KKSSJJ1112/ZUTOMAYO_mirror_shooter/사진/4.jpg

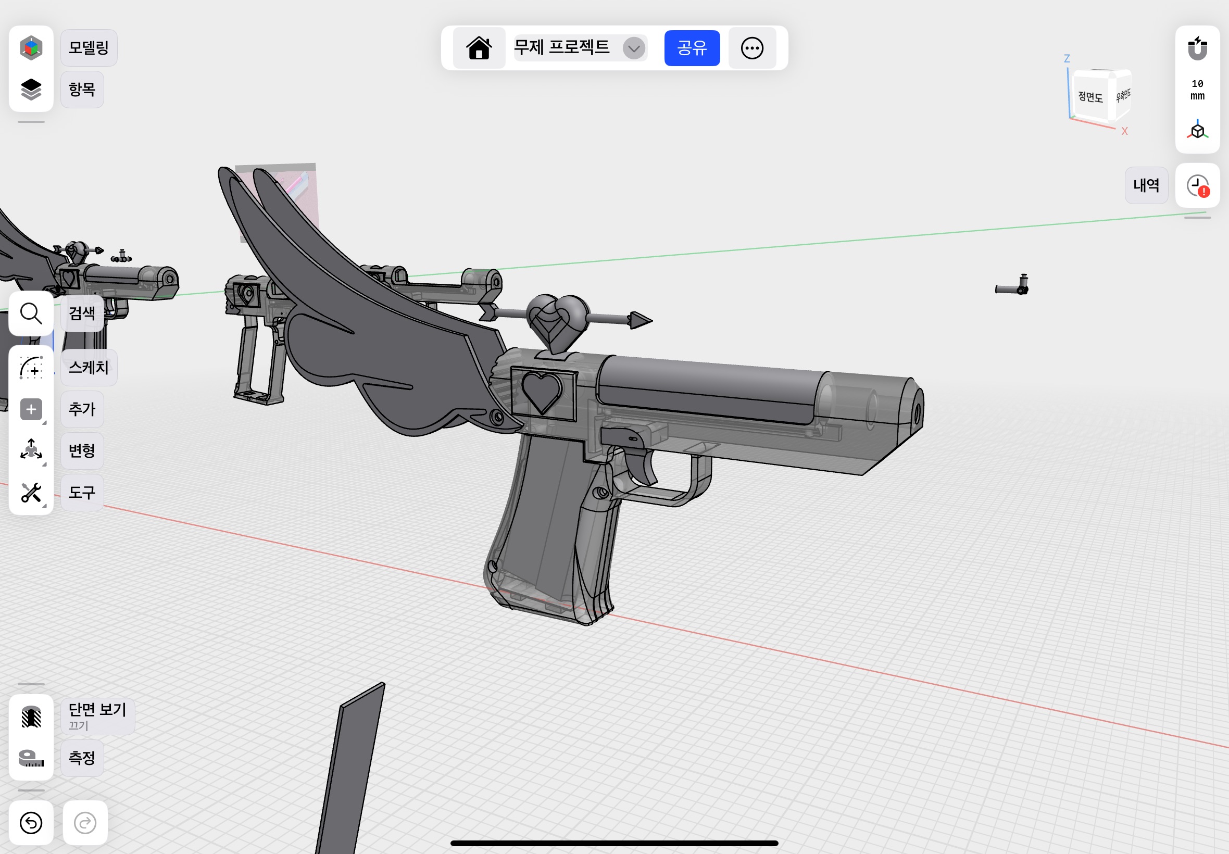
사진/4.jpg
