KKSSJJ1112/ZUTOMAYO_mirror_shooter/사진/6.jpg

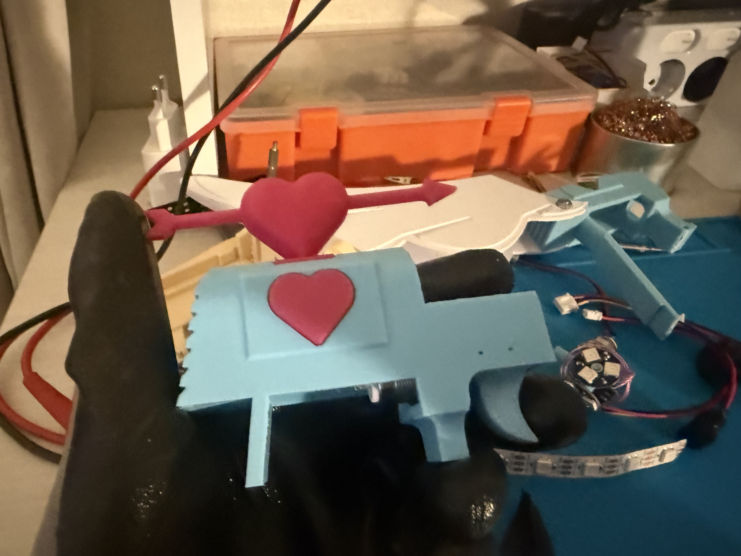
사진/6.jpg
