KKSSJJ1112/ZUTOMAYO_mirror_shooter/사진/8.jpg

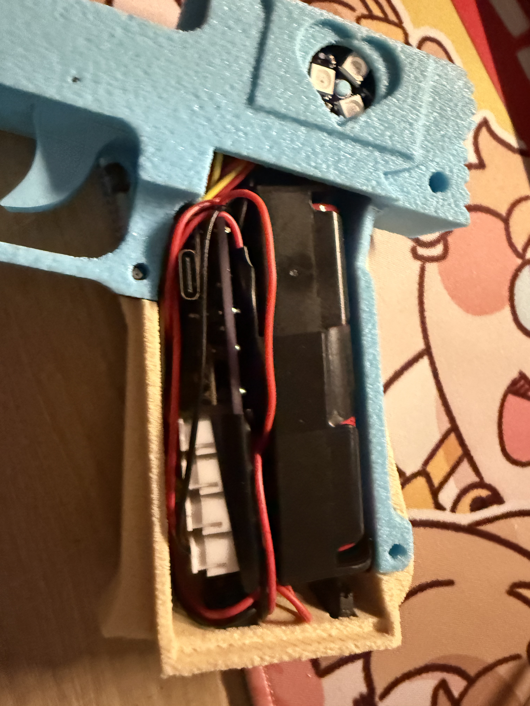
사진/8.jpg
