KKSSJJ1112/ZUTOMAYO_mirror_shooter/사진/ffa.png

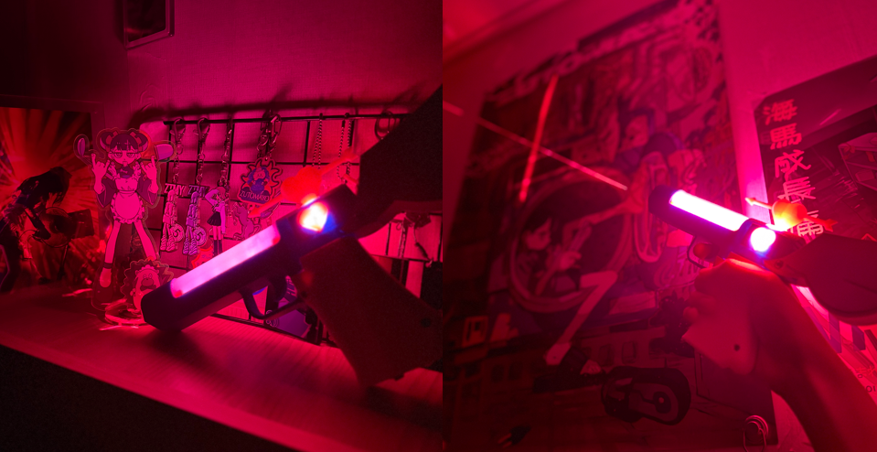
사진/ffa.png
