KKSSJJ1112/ZUTOMAYO_mirror_shooter/사진/KakaoTalk_20250901_193324154_01.jpg

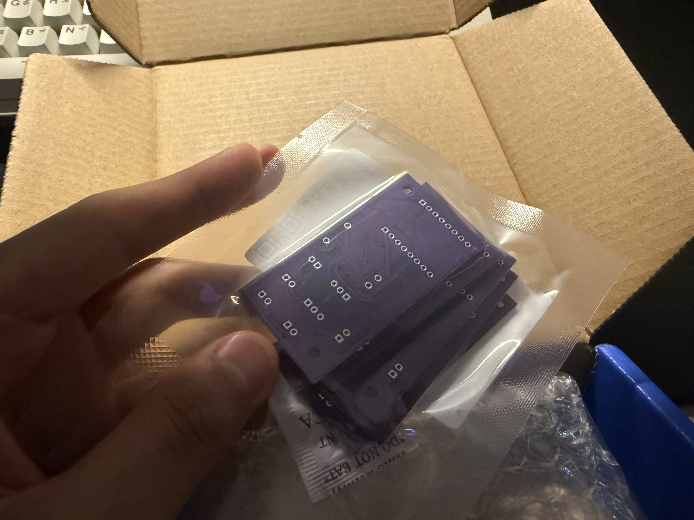
사진/KakaoTalk_20250901_193324154_01.jpg
