KKSSJJ1112/ZUTOMAYO_mirror_shooter/사진/KakaoTalk_20251231_225942691_02.jpg

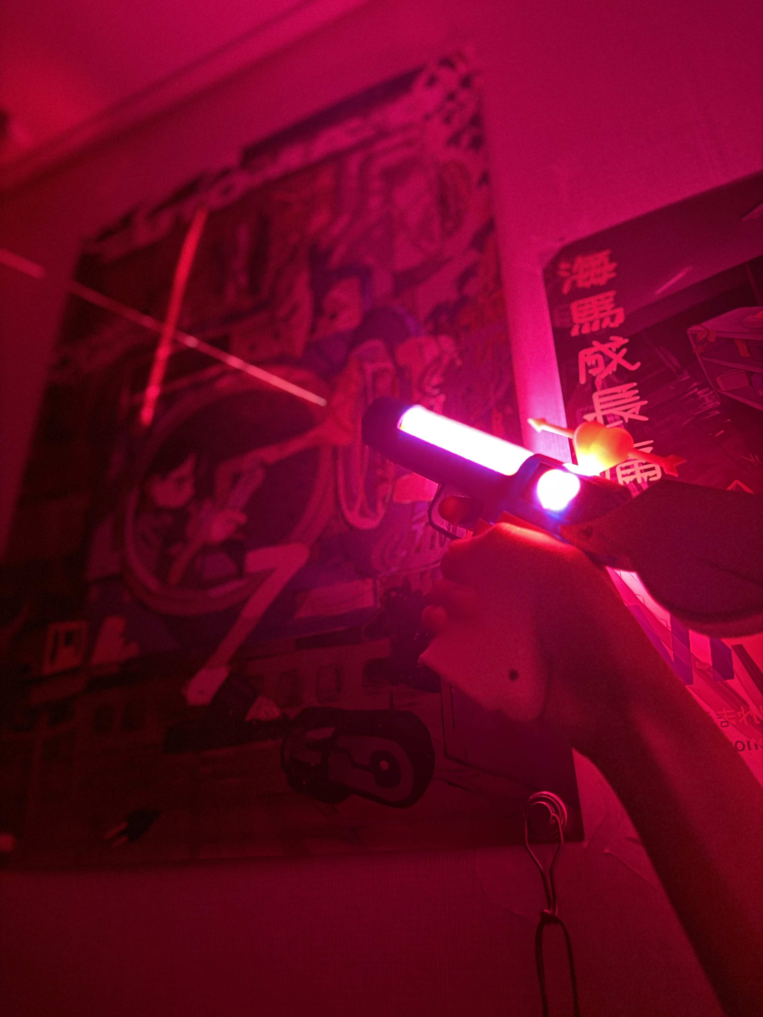
사진/KakaoTalk_20251231_225942691_02.jpg
