KKSSJJ1112/ZUTOMAYO_mirror_shooter/mirrorshooter_stl/____final/blue/ring holder.stl

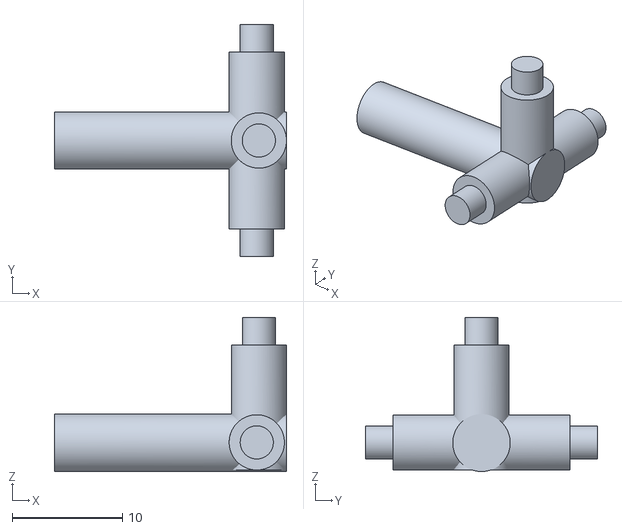
[picture p34: CAD file, 2025-11-05]
mirrorshooter_stl/____final/blue/ring holder.stl
21.0 x 21.0 x 13.9
