KKSSJJ1112/ZUTOMAYO_mirror_shooter/mirrorshooter_stl/____final/trans pink/small heart.stl

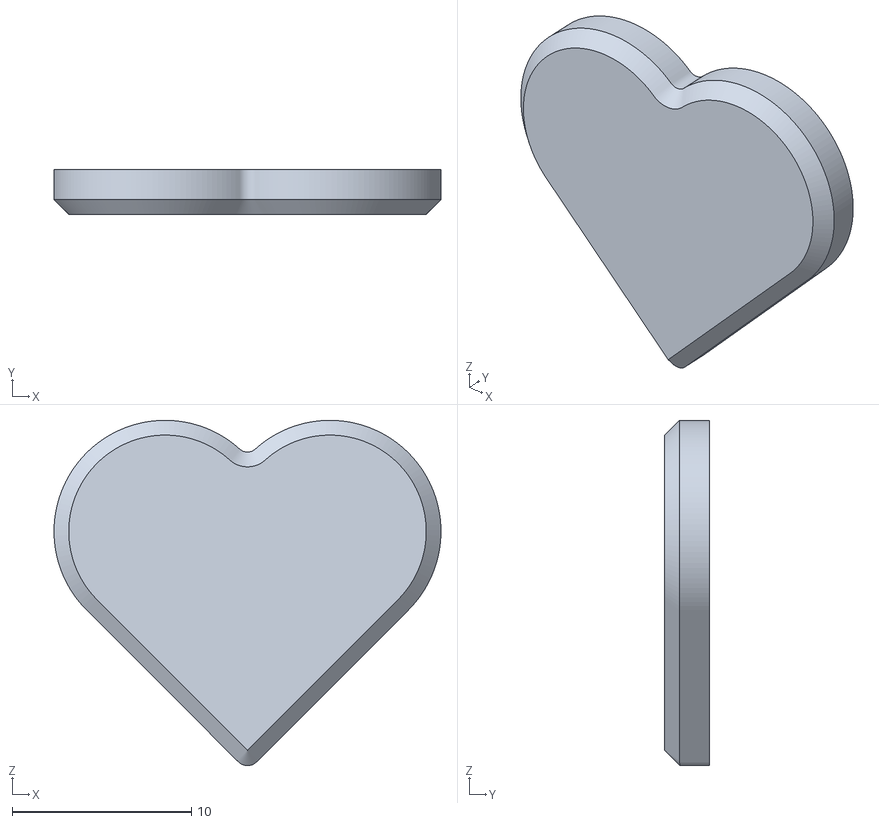
[picture p35: CAD file, 2025-11-05]
mirrorshooter_stl/____final/trans pink/small heart.stl
21.6 x 2.50 x 19.3
