KKSSJJ1112/ZUTOMAYO_mirror_shooter/mirrorshooter_stl/test/second_test/blue/ring holder ttesst.stl

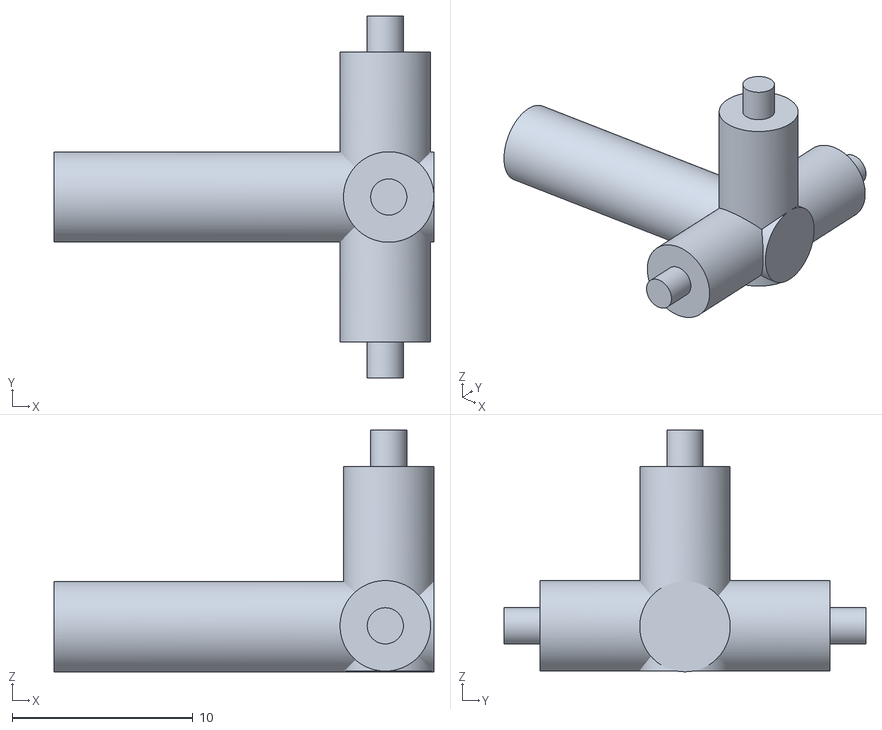
[picture p36: CAD file, 2025-11-05]
mirrorshooter_stl/test/second_test/blue/ring holder ttesst.stl
21.0 x 20.0 x 13.4
