KKSSJJ1112/ZUTOMAYO_mirror_shooter/mirrorshooter_stl/test/second_test/trans_pink/cover test.stl

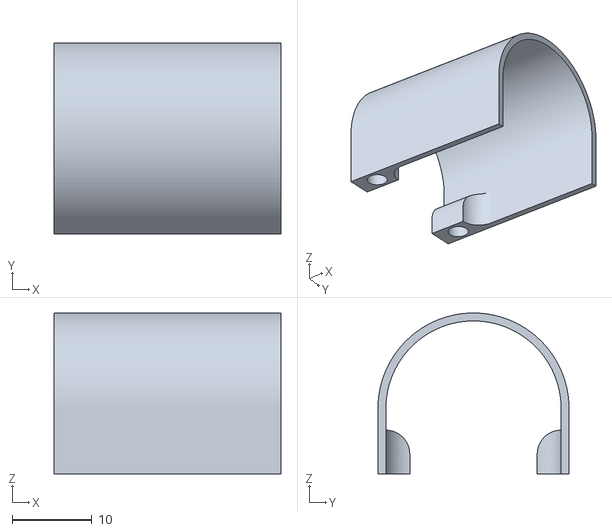
[picture p37: CAD file, 2025-11-05]
mirrorshooter_stl/test/second_test/trans_pink/cover test.stl
28.5 x 24.0 x 20.2
