KKSSJJ1112/ZUTOMAYO_mirror_shooter/mirrorshooter_stl/____final/trans pink/cover.stl

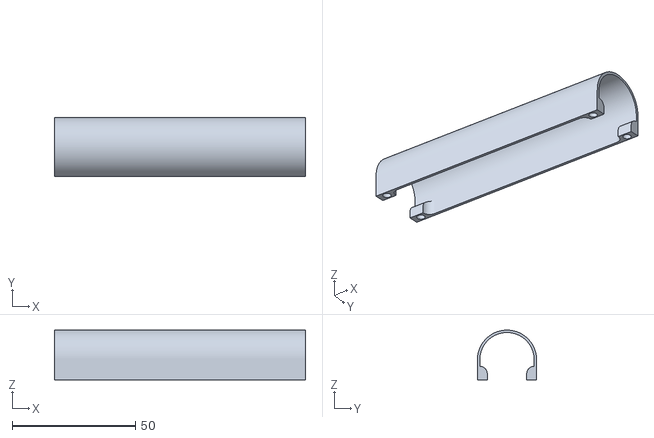
[picture p38: CAD file, 2025-11-05]
mirrorshooter_stl/____final/trans pink/cover.stl
101.8 x 24.0 x 20.2
