KKSSJJ1112/ZUTOMAYO_mirror_shooter/mirrorshooter_stl/test/first_test/trigger_test/triger-sub-invisible.stl

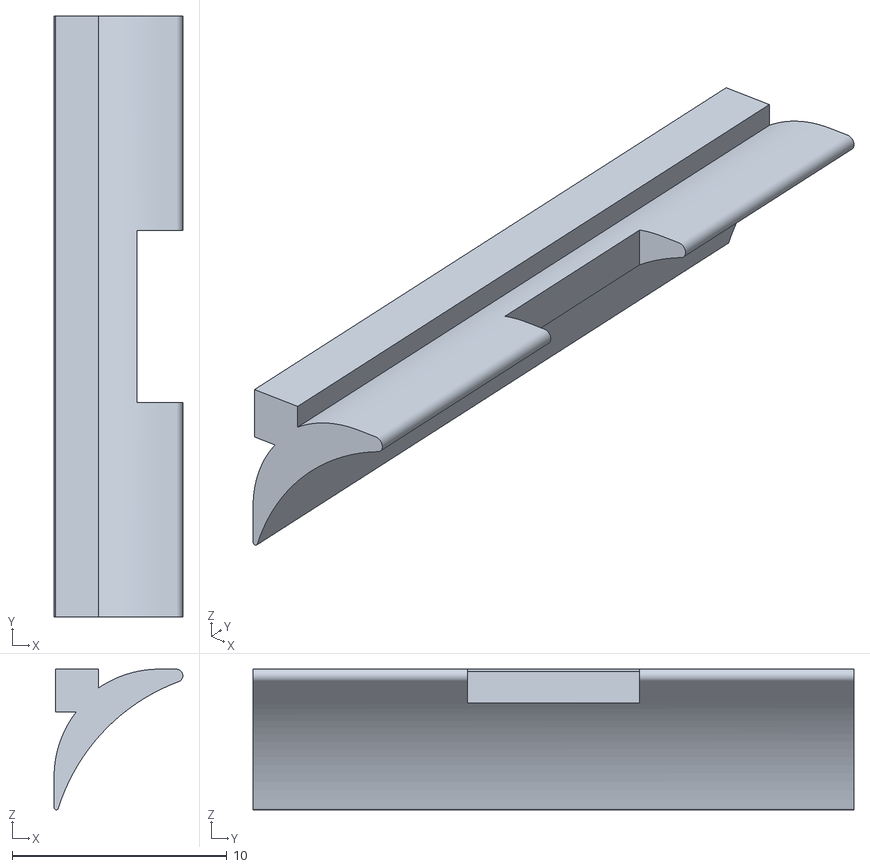
[picture p39: CAD file, 2025-11-05]
mirrorshooter_stl/test/first_test/trigger_test/triger-sub-invisible.stl
6.00 x 28.0 x 6.56
