KKSSJJ1112/ZUTOMAYO_mirror_shooter/mirrorshooter_stl/test/second_test/blue/trigger test.stl

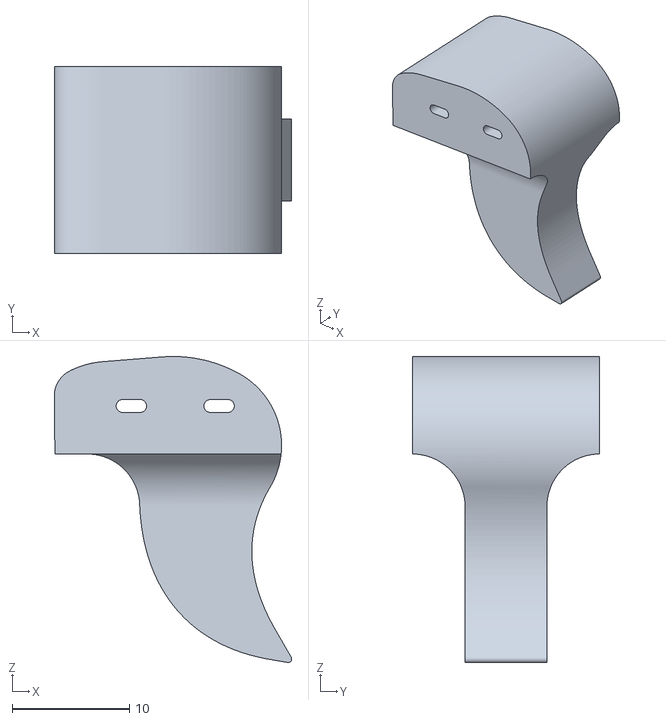
[picture p40: CAD file, 2025-11-05]
mirrorshooter_stl/test/second_test/blue/trigger test.stl
20.3 x 16.0 x 26.2
