KKSSJJ1112/ZUTOMAYO_mirror_shooter/mirrorshooter_stl/test/second_test/trans_pink/small heart test.stl

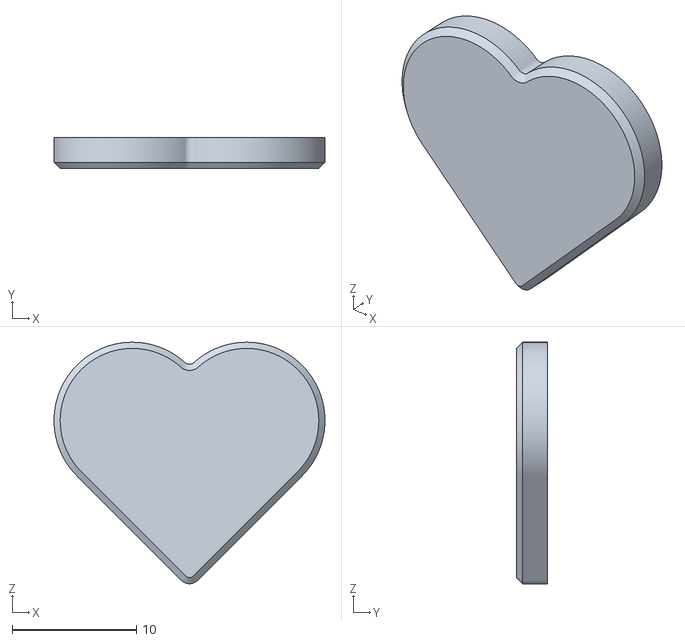
[picture p41: CAD file, 2025-11-05]
mirrorshooter_stl/test/second_test/trans_pink/small heart test.stl
21.8 x 2.50 x 19.4
