KKSSJJ1112/ZUTOMAYO_mirror_shooter/mirrorshooter_stl/____final/blue/trigger.stl

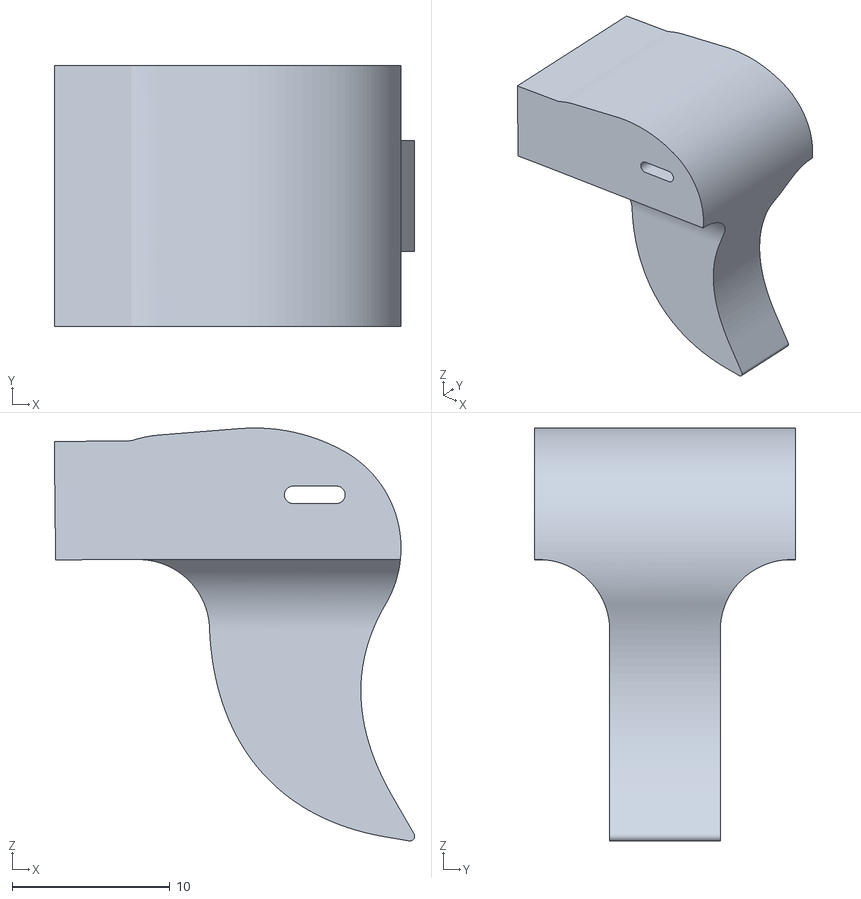
[picture p42: CAD file, 2025-11-05]
mirrorshooter_stl/____final/blue/trigger.stl
22.8 x 16.5 x 26.2
