KKSSJJ1112/ZUTOMAYO_mirror_shooter/mirrorshooter_stl/test/3rd_test/grib-lll.stl

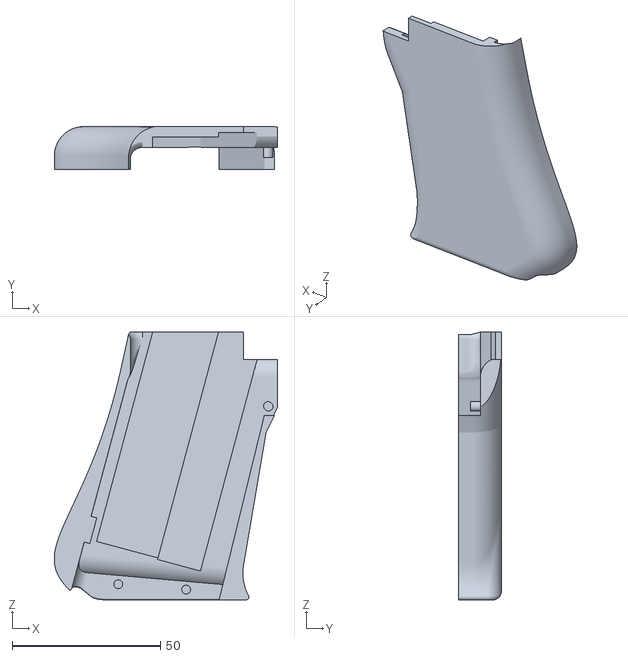
[picture p43: CAD file, 2025-11-05]
mirrorshooter_stl/test/3rd_test/grib-lll.stl
75.5 x 14.5 x 90.5
