KKSSJJ1112/ZUTOMAYO_mirror_shooter/mirrorshooter_stl/test/first_test/trigger_test/triger-triger.stl

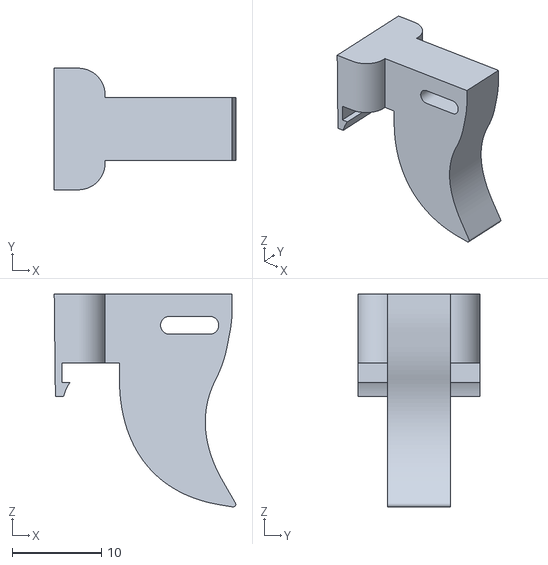
[picture p44: CAD file, 2025-11-05]
mirrorshooter_stl/test/first_test/trigger_test/triger-triger.stl
20.3 x 13.6 x 23.8
