KKSSJJ1112/ZUTOMAYO_mirror_shooter/mirrorshooter_stl/test/second_test/blue/ring holder 4.stl

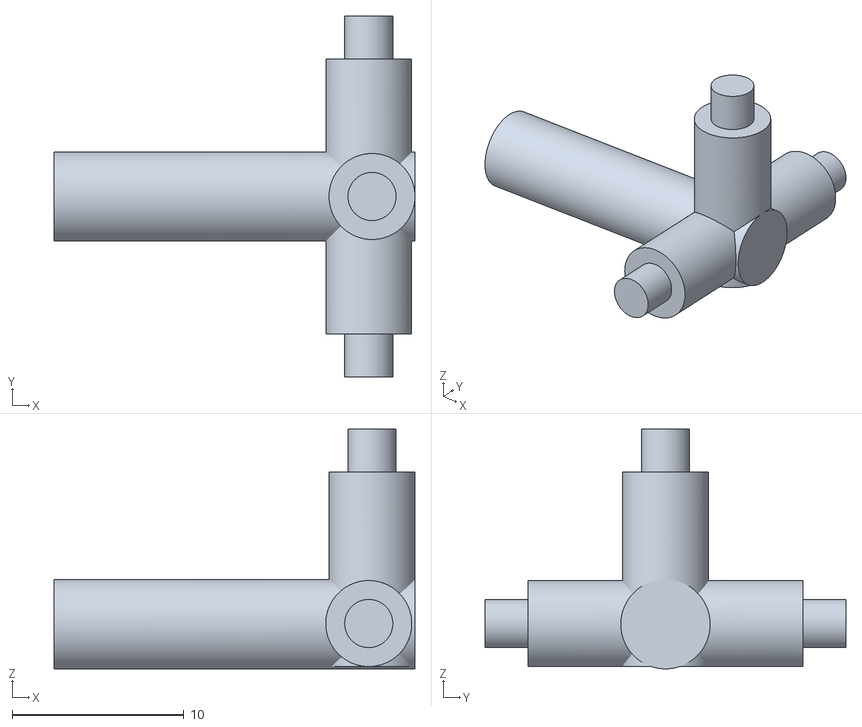
[picture p45: CAD file, 2025-11-05]
mirrorshooter_stl/test/second_test/blue/ring holder 4.stl
21.0 x 21.0 x 14.0
