KKSSJJ1112/ZUTOMAYO_mirror_shooter/mirrorshooter_stl/test/second_test/trans_pink/small heart 2.stl

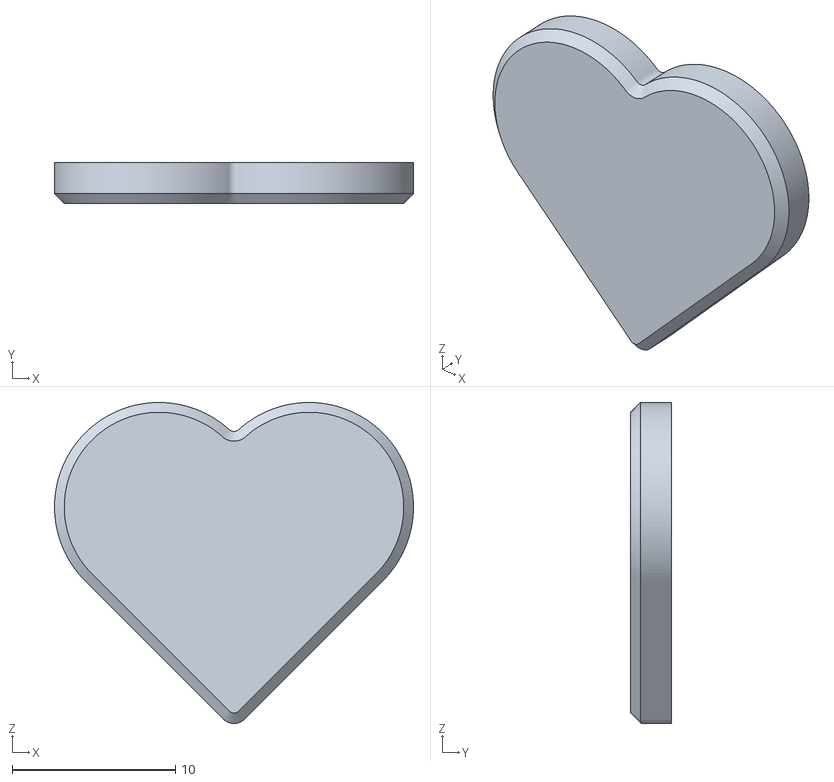
[picture p46: CAD file, 2025-11-05]
mirrorshooter_stl/test/second_test/trans_pink/small heart 2.stl
22.0 x 2.50 x 19.7
