KKSSJJ1112/ZUTOMAYO_mirror_shooter/mirrorshooter_stl/test/second_test/blue/trigger test 4.stl

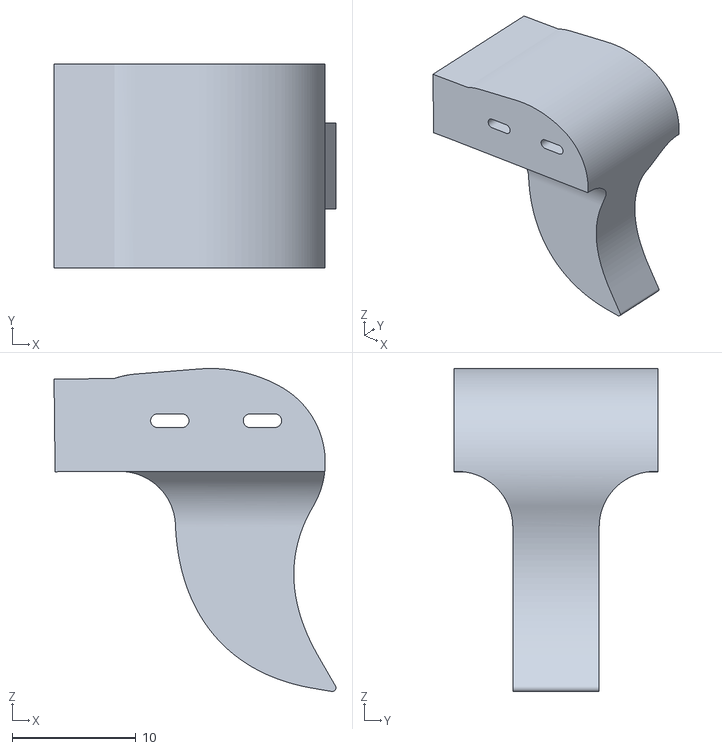
[picture p47: CAD file, 2025-11-05]
mirrorshooter_stl/test/second_test/blue/trigger test 4.stl
22.8 x 16.5 x 26.2
